PaulKlinger/CATreus/kbd_firmware/src/bluetooth.c

#include "bluetooth.h"

#include <assert.h>
#include <bluetooth/services/hids.h>
#include <errno.h>
#include <soc.h>
#include <stddef.h>
#include <string.h>
#include <zephyr/bluetooth/bluetooth.h>
#include <zephyr/bluetooth/conn.h>
#include <zephyr/bluetooth/gatt.h>
#include <zephyr/bluetooth/hci.h>
#include <zephyr/bluetooth/services/bas.h>
#include <zephyr/bluetooth/services/dis.h>
#include <zephyr/bluetooth/uuid.h>
#include <zephyr/drivers/gpio.h>
#include <zephyr/kernel.h>
#include <zephyr/settings/settings.h>
#include <zephyr/spinlock.h>
#include <zephyr/sys/byteorder.h>
#include <zephyr/sys/printk.h>
#include <zephyr/types.h>

#include "config.h"
#include "key_layout.h"
#include "leds.h"
#include "ui.h"

#define DEVICE_NAME CONFIG_BT_DEVICE_NAME
#define DEVICE_NAME_LEN (sizeof(DEVICE_NAME) - 1)

#define BASE_USB_HID_SPEC_VERSION 0x0101

#define OUTPUT_REPORT_MAX_LEN 1
#define OUTPUT_REPORT_BIT_MASK_CAPS_LOCK 0x02
#define INPUT_REP_KEYS_REF_ID 0
#define OUTPUT_REP_KEYS_REF_ID 0
#define MODIFIER_KEY_POS 0
#define SHIFT_KEY_CODE 0x02
#define SCAN_CODE_POS 2
#define KEYS_MAX_LEN (INPUT_REPORT_KEYS_MAX_LEN - SCAN_CODE_POS)

/* HIDs queue elements. */
#define HIDS_QUEUE_SIZE 10

/* ********************* */
/* Buttons configuration */

/* Note: The configuration below is the same as BOOT mode configuration
 * This simplifies the code as the BOOT mode is the same as REPORT mode.
 * Changing this configuration would require separate implementation of
 * BOOT mode report generation.
 */
#define KEY_CTRL_CODE_MIN 224 /* Control key codes - required 8 of them */
#define KEY_CTRL_CODE_MAX 231 /* Control key codes - required 8 of them */
#define KEY_CODE_MIN 0        /* Normal key codes */
#define KEY_CODE_MAX 101      /* Normal key codes */
#define KEY_PRESS_MAX                     \
  6 /* Maximum number of non-control keys \
     * pressed simultaneously             \
     */

/* Number of bytes in key report
 *
 * 1B - control keys
 * 1B - reserved
 * rest - non-control keys
 */
#define INPUT_REPORT_KEYS_MAX_LEN (1 + 1 + KEY_PRESS_MAX)

/* Current report map construction requires exactly 8 buttons */
BUILD_ASSERT((KEY_CTRL_CODE_MAX - KEY_CTRL_CODE_MIN) + 1 == 8);

/* OUT report internal indexes.
 *
 * This is a position in internal report table and is not related to
 * report ID.
 */
enum { OUTPUT_REP_KEYS_IDX = 0 };

/* INPUT report internal indexes.
 *
 * This is a position in internal report table and is not related to
 * report ID.
 */
enum { INPUT_REP_KEYS_IDX = 0 };

/* HIDS instance. */
BT_HIDS_DEF(hids_obj, OUTPUT_REPORT_MAX_LEN, INPUT_REPORT_KEYS_MAX_LEN);

static volatile bool is_adv;
static volatile bool waiting_for_passkey_confirmation = false;

static const struct bt_data ad[] = {
    BT_DATA_BYTES(BT_DATA_GAP_APPEARANCE,
                  (CONFIG_BT_DEVICE_APPEARANCE >> 0) & 0xff,
                  (CONFIG_BT_DEVICE_APPEARANCE >> 8) & 0xff),
    BT_DATA_BYTES(BT_DATA_FLAGS, (BT_LE_AD_GENERAL | BT_LE_AD_NO_BREDR)),
    BT_DATA_BYTES(BT_DATA_UUID16_ALL, BT_UUID_16_ENCODE(BT_UUID_HIDS_VAL),
                  BT_UUID_16_ENCODE(BT_UUID_BAS_VAL)),
};

static const struct bt_data sd[] = {
    BT_DATA(BT_DATA_NAME_COMPLETE, DEVICE_NAME, DEVICE_NAME_LEN),
};

static struct bt_conn *current_conn = NULL;

static struct k_work adv_work;

struct addr get_current_addr() {
  struct addr addr;
  if (current_conn) {
    bt_addr_le_to_str(bt_conn_get_dst(current_conn), addr.addr,
                      sizeof(addr.addr));
  }
  return addr;
}

static void advertising_start(void) { k_work_submit(&adv_work); }

static void adv_work_handler(struct k_work *work) {
  int err;
  const struct bt_le_adv_param *adv_param =
      BT_LE_ADV_PARAM(BT_LE_ADV_OPT_CONN, BT_GAP_ADV_FAST_INT_MIN_2,
                      BT_GAP_ADV_FAST_INT_MAX_2, NULL);

  err = bt_le_adv_start(adv_param, ad, ARRAY_SIZE(ad), sd, ARRAY_SIZE(sd));
  if (err) {
    if (err == -EALREADY) {
      printk("Advertising continued\n");
    } else {
      printk("Advertising failed to start (err %d)\n", err);
    }

    return;
  }

  is_adv = true;
  led_start_advertising_anim();
  printk("Advertising successfully started\n");
}

static void connected(struct bt_conn *conn, uint8_t err) {
  char addr[BT_ADDR_LE_STR_LEN];

  bt_addr_le_to_str(bt_conn_get_dst(conn), addr, sizeof(addr));

  if (err) {
    printk("Failed to connect to %s 0x%02x %s\n", addr, err,
           bt_hci_err_to_str(err));
    return;
  }
  current_conn = bt_conn_ref(conn);

  printk("Connected %s\n", addr);

  err = bt_hids_connected(&hids_obj, conn);

  if (err) {
    printk("Failed to notify HID service about connection\n");
    return;
  }

  is_adv = false;
  led_stop_anim();
  int ret = bt_conn_set_security(conn, BT_SECURITY_L4);
  if (ret) {
    printk("Failed to set security to L4 (%d), trying L3\n", ret);
    ret = bt_conn_set_security(conn, BT_SECURITY_L3);
    if (ret) {
      printk("Failed to set security to L3: %d\n", ret);
    }
  }

  init_key_layout();
}

static void disconnected(struct bt_conn *conn, uint8_t reason) {
  char addr[BT_ADDR_LE_STR_LEN];

  bt_addr_le_to_str(bt_conn_get_dst(conn), addr, sizeof(addr));

  printk("Disconnected from %s, reason 0x%02x %s\n", addr, reason,
         bt_hci_err_to_str(reason));
  int err = bt_hids_disconnected(&hids_obj, conn);

  if (err) {
    printk("Failed to notify HID service about disconnection\n");
  }
  bt_conn_unref(current_conn);
  current_conn = NULL;
  advertising_start();
}

static void security_changed(struct bt_conn *conn, bt_security_t level,
                             enum bt_security_err err) {
  char addr[BT_ADDR_LE_STR_LEN];

  bt_addr_le_to_str(bt_conn_get_dst(conn), addr, sizeof(addr));

  if (!err) {
    printk("Security changed: %s level %u\n", addr, level);
  } else {
    printk("Security failed: %s level %u err %d %s\n", addr, level, err,
           bt_security_err_to_str(err));
  }
}

BT_CONN_CB_DEFINE(conn_callbacks) = {
    .connected = connected,
    .disconnected = disconnected,
    .security_changed = security_changed,
};

static void auth_passkey_display(struct bt_conn *conn, unsigned int passkey) {
  if (conn != current_conn) {
    if (current_conn) {
      bt_conn_unref(current_conn);
    }
    current_conn = bt_conn_ref(conn);
  }
  ui_send_display_passkey(passkey);
}

static void auth_passkey_confirm(struct bt_conn *conn, unsigned int passkey) {
  if (conn != current_conn) {
    if (current_conn) {
      bt_conn_unref(current_conn);
    }
    current_conn = bt_conn_ref(conn);
  }
  waiting_for_passkey_confirmation = true;
  ui_send_confirm_passkey(passkey);
}

static void auth_cancel(struct bt_conn *conn) {
  char addr[BT_ADDR_LE_STR_LEN];

  bt_addr_le_to_str(bt_conn_get_dst(conn), addr, sizeof(addr));

  printk("Pairing cancelled: %s\n", addr);
  if (current_conn) {
    bt_conn_unref(current_conn);
    current_conn = NULL;
  }
}

static void pairing_complete(struct bt_conn *conn, bool bonded) {
  char addr[BT_ADDR_LE_STR_LEN];

  bt_addr_le_to_str(bt_conn_get_dst(conn), addr, sizeof(addr));

  printk("Pairing completed: %s, bonded: %d\n", addr, bonded);
}

static void pairing_failed(struct bt_conn *conn, enum bt_security_err reason) {
  char addr[BT_ADDR_LE_STR_LEN];

  bt_addr_le_to_str(bt_conn_get_dst(conn), addr, sizeof(addr));

  printk("Pairing failed conn: %s, reason %d %s\n", addr, reason,
         bt_security_err_to_str(reason));
}

static struct bt_conn_auth_cb conn_auth_callbacks = {
    .passkey_display = auth_passkey_display,
    .passkey_confirm = auth_passkey_confirm,
    .cancel = auth_cancel,
};

static struct bt_conn_auth_info_cb conn_auth_info_callbacks = {
    .pairing_complete = pairing_complete, .pairing_failed = pairing_failed};

static void num_comp_reply(bool accept) {
  char addr[BT_ADDR_LE_STR_LEN];

  bt_addr_le_to_str(bt_conn_get_dst(current_conn), addr, sizeof(addr));
  printk("num_comp_reply(%d), conn: %s\n", accept, addr);
  if (accept) {
    bt_conn_auth_passkey_confirm(current_conn);
    printk("Numeric Match, conn %p\n", current_conn);
  } else {
    bt_conn_auth_cancel(current_conn);
    printk("Numeric Reject, conn %p\n", current_conn);
    bt_conn_unref(current_conn);
  }
}

void confirm_passkey(void) {
  num_comp_reply(true);
  waiting_for_passkey_confirmation = false;
}

void reject_passkey(void) {
  num_comp_reply(false);
  waiting_for_passkey_confirmation = false;
}

bool ble_is_advertising() { return is_adv; }

bool ble_is_connected() { return current_conn != NULL; }

bool is_waiting_for_passkey_confirmation() {
  return waiting_for_passkey_confirmation;
}

static void init_hid(void) {
  int err;
  struct bt_hids_init_param hids_init_obj = {0};
  struct bt_hids_inp_rep *hids_inp_rep;
  struct bt_hids_outp_feat_rep *hids_outp_rep;

  static const uint8_t report_map[] = {
      0x05, 0x01, /* Usage Page (Generic Desktop) */
      0x09, 0x06, /* Usage (Keyboard) */
      0xA1, 0x01, /* Collection (Application) */

  /* Keys */
#if INPUT_REP_KEYS_REF_ID
      0x85, INPUT_REP_KEYS_REF_ID,
#endif
      0x05, 0x07, /* Usage Page (Key Codes) */
      0x19, 0xe0, /* Usage Minimum (224) */
      0x29, 0xe7, /* Usage Maximum (231) */
      0x15, 0x00, /* Logical Minimum (0) */
      0x25, 0x01, /* Logical Maximum (1) */
      0x75, 0x01, /* Report Size (1) */
      0x95, 0x08, /* Report Count (8) */
      0x81, 0x02, /* Input (Data, Variable, Absolute) */

      0x95, 0x01, /* Report Count (1) */
      0x75, 0x08, /* Report Size (8) */
      0x81, 0x01, /* Input (Constant) reserved byte(1) */

      0x95, 0x06, /* Report Count (6) */
      0x75, 0x08, /* Report Size (8) */
      0x15, 0x00, /* Logical Minimum (0) */
      0x25, 0x65, /* Logical Maximum (101) */
      0x05, 0x07, /* Usage Page (Key codes) */
      0x19, 0x00, /* Usage Minimum (0) */
      0x29, 0x65, /* Usage Maximum (101) */
      0x81, 0x00, /* Input (Data, Array) Key array(6 bytes) */

  /* LED */
#if OUTPUT_REP_KEYS_REF_ID
      0x85, OUTPUT_REP_KEYS_REF_ID,
#endif
      0x95, 0x05, /* Report Count (5) */
      0x75, 0x01, /* Report Size (1) */
      0x05, 0x08, /* Usage Page (Page# for LEDs) */
      0x19, 0x01, /* Usage Minimum (1) */
      0x29, 0x05, /* Usage Maximum (5) */
      0x91, 0x02, /* Output (Data, Variable, Absolute), */
                  /* Led report */
      0x95, 0x01, /* Report Count (1) */
      0x75, 0x03, /* Report Size (3) */
      0x91, 0x01, /* Output (Data, Variable, Absolute), */
                  /* Led report padding */

      0xC0 /* End Collection (Application) */
  };

  hids_init_obj.rep_map.data = report_map;
  hids_init_obj.rep_map.size = sizeof(report_map);

  hids_init_obj.info.bcd_hid = BASE_USB_HID_SPEC_VERSION;
  hids_init_obj.info.b_country_code = 0x00;
  hids_init_obj.info.flags =
      (BT_HIDS_REMOTE_WAKE | BT_HIDS_NORMALLY_CONNECTABLE);

  hids_inp_rep = &hids_init_obj.inp_rep_group_init.reports[INPUT_REP_KEYS_IDX];
  hids_inp_rep->size = INPUT_REPORT_KEYS_MAX_LEN;
  hids_inp_rep->id = INPUT_REP_KEYS_REF_ID;
  hids_init_obj.inp_rep_group_init.cnt++;

  hids_outp_rep =
      &hids_init_obj.outp_rep_group_init.reports[OUTPUT_REP_KEYS_IDX];
  hids_outp_rep->size = OUTPUT_REPORT_MAX_LEN;
  hids_outp_rep->id = OUTPUT_REP_KEYS_REF_ID;
  hids_init_obj.outp_rep_group_init.cnt++;

  hids_init_obj.is_kb = true;

  err = bt_hids_init(&hids_obj, &hids_init_obj);
  __ASSERT(err == 0, "HIDS initialization failed\n");
}

int init_bluetooth(void) {
  waiting_for_passkey_confirmation = false;
  int err;

  err = bt_conn_auth_cb_register(&conn_auth_callbacks);
  if (err) {
    printk("Failed to register authorization callbacks.\n");
    return err;
  }

  err = bt_conn_auth_info_cb_register(&conn_auth_info_callbacks);
  if (err) {
    printk("Failed to register authorization info callbacks.\n");
    return err;
  }

  init_hid();

  err = bt_enable(NULL);
  if (err) {
    printk("Bluetooth init failed (err %d)\n", err);
    return err;
  }

  printk("Bluetooth initialized\n");

  if (IS_ENABLED(CONFIG_SETTINGS)) {
    settings_load();
  }

  k_work_init(&adv_work, adv_work_handler);
  advertising_start();
  return 0;
}

void send_encoded_keys(struct encoded_keys keys) {
  /* HID Report:
   * Byte 0: modifier mask
   * Byte 1: reserved (must be 0)
   * Byte 2-7: keys (up to 6 keys)
   */
  uint8_t report[8] = {0};

  report[0] = keys.modifier_mask;
  report[1] = 0;  // reserved byte, always 0

  for (int i = 0; i < MAX_N_ENCODED_KEYS; i++) {
    report[i + 2] = keys.keys[i];
  }
  int ret = bt_hids_inp_rep_send(&hids_obj, current_conn, INPUT_REP_KEYS_IDX,
                                 report, sizeof(report), NULL);
  printk("HID report sent, ret: %d\n", ret);
}

void send_bas_soc(float soc) { bt_bas_set_battery_level((uint8_t)soc); }
