PaulKlinger/CATreus/kbd_firmware/src/anim_idle.c

#include "anim_idle.h"
const uint8_t idle_frames[38][8][128] = {
{
{255,255,255,255,255,255,255,255,255,255,255,255,255,255,255,255,255,255,255,255,255,255,255,255,255,255,255,255,255,255,255,255,7,7,0,0,224,224,129,129,7,7,31,31,127,127,255,255,127,127,127,127,127,127,127,127,127,127,127,127,127,127,255,255,127,127,31,31,7,7,129,129,224,224,0,0,7,7,255,255,255,255,255,255,255,255,255,255,255,255,255,255,255,255,255,255,255,255,255,255,255,255,255,255,255,255,255,255,255,255,255,255,255,255,255,255,255,255,255,255,255,255,255,255,255,255,255,255},
{255,255,255,255,255,255,255,255,255,255,255,255,255,255,255,255,255,255,255,255,255,255,255,255,255,255,255,255,255,255,255,255,224,224,0,0,7,7,31,31,30,30,0,0,0,0,25,25,24,24,96,96,0,0,0,0,0,0,96,96,24,24,25,25,0,0,0,0,30,30,31,31,7,7,0,0,224,224,255,255,255,255,255,255,255,255,255,255,255,255,255,255,255,255,255,255,255,255,255,255,255,255,255,255,255,255,255,255,255,255,255,255,255,255,255,255,255,255,255,255,255,255,255,255,255,255,255,255},
{255,255,255,255,255,255,255,255,255,255,255,255,255,255,255,255,255,255,255,255,255,255,255,255,255,255,255,255,255,255,255,255,127,127,6,6,0,0,0,0,224,224,24,24,6,6,6,6,24,24,224,224,0,0,0,0,0,0,224,224,24,24,6,6,6,6,24,24,224,224,0,0,0,0,6,6,127,127,255,255,255,255,255,255,255,255,255,255,255,255,255,255,255,255,255,255,255,255,255,255,255,255,255,255,255,255,255,255,255,255,255,255,255,255,255,255,255,255,255,255,255,255,255,255,255,255,255,255},
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
