PaulKlinger/CATreus/kbd_firmware/src/anim_sleep.c

#include "anim_sleep.h"
const uint8_t sleep_frames[15][8][128] = {
{
{255,255,255,255,255,255,255,255,255,255,255,255,255,255,255,255,255,255,255,255,255,255,255,255,255,255,255,255,255,255,255,255,7,7,0,0,224,224,129,129,7,7,31,31,127,127,255,255,127,127,127,127,127,127,127,127,127,127,127,127,127,127,255,255,127,127,31,31,7,7,129,129,224,224,0,0,7,7,255,255,255,255,255,255,255,255,255,255,255,255,255,255,255,255,255,255,255,255,255,255,255,255,255,255,255,255,255,255,255,255,255,255,255,255,255,255,255,255,255,255,255,255,255,255,255,255,255,255},
{255,255,255,255,255,255,255,255,255,255,255,255,255,255,255,255,255,255,255,255,255,255,255,255,255,255,255,255,255,255,255,255,224,224,0,0,7,7,31,31,30,30,0,0,0,0,25,25,24,24,96,96,0,0,0,0,0,0,96,96,24,24,25,25,0,0,0,0,30,30,31,31,7,7,0,0,224,224,255,255,255,255,255,255,255,255,255,255,255,255,255,255,255,255,255,255,255,255,255,255,255,255,255,255,255,255,255,255,255,255,255,255,255,255,255,255,255,255,255,255,255,255,255,255,255,255,255,255},
{255,255,255,255,255,255,255,255,255,255,255,255,255,255,255,255,255,255,255,255,255,255,255,255,255,255,255,255,255,255,255,255,127,127,6,6,0,0,0,0,224,224,24,24,6,6,6,6,24,24,224,224,0,0,0,0,0,0,224,224,24,24,6,6,6,6,24,24,224,224,0,0,0,0,6,6,127,127,255,255,255,255,255,255,255,255,255,255,255,255,255,255,255,255,255,255,255,255,255,255,255,255,255,255,255,255,255,255,255,255,255,255,255,255,255,255,255,255,255,255,255,255,255,255,255,255,255,255},
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
},};
const uint8_t sleep_frame_counts[SLEEP_N_FRAMES] = {2,4,1,1,1,1,1,1,2,1,1,2,8,8,8};

struct animation anim_sleep = {
    .frames = sleep_frames,
    .frame_counts = sleep_frame_counts,
    .frame_step = 1,
    .start_idx = 0,
    .end_idx = 14,
    .init_idx = 0,
    .loop = false,
};
