PaulKlinger/CATreus/kbd_firmware/src/config.h

#ifndef CONFIG_H
#define CONFIG_H

#include <stdbool.h>
#include <stdint.h>

#define MAX_N_ENCODED_KEYS 6
#define MAX_N_PRESSED_KEYS 6
// go to sleep if no key presses for this time
#define DEEP_SLEEP_TIMEOUT_S 60 * 30
// go to sleep if no key presses and keyboard is advertising
#define DEEP_SLEEP_ADVERTISING_TIMEOUT_S 60 * 5
// go to sleep if constant key presses for this time
// (to prevent battery drain if something is lying on the keyboard)
#define DEEP_SLEEP_NO_PRESSED_TIMEOUT_S 60 * 5

// send state of charge once per minute
#define BAS_SOC_INTERVAL_S 60

struct key_coord {
  uint8_t row;
  uint8_t col;
};

inline bool keq(struct key_coord a, struct key_coord b) {
  return a.row == b.row && a.col == b.col;
}

// physical keys pressed
struct pressed_keys {
  bool wake_pressed;
  struct key_coord keys[MAX_N_PRESSED_KEYS];
  uint8_t n_pressed;
};

// keys encoded for USB HID report
struct encoded_keys {
  uint8_t modifier_mask;
  uint8_t keys[MAX_N_ENCODED_KEYS];
};

#endif  // CONFIG_H
