PaulKlinger/CATreus/kbd_firmware/src/key_matrix.h

#ifndef KEY_MATRIX_H
#define KEY_MATRIX_H

#include <stdbool.h>
#include <stdint.h>

#include "config.h"

void read_key_matrix(void);

void init_key_matrix(void);

bool wake_pressed(void);

int wait_for_key(int timeout_ms);

extern struct pressed_keys current_pressed_keys;
extern struct pressed_keys last_pressed_keys;

#endif  // KEY_MATRIX_H
